mhzkb/another-space/1.5/and-another-space/and-another-space.kicad_sch

## KiCad design 1.5/and-another-space/and-another-space.kicad_sch (2025-10-27)

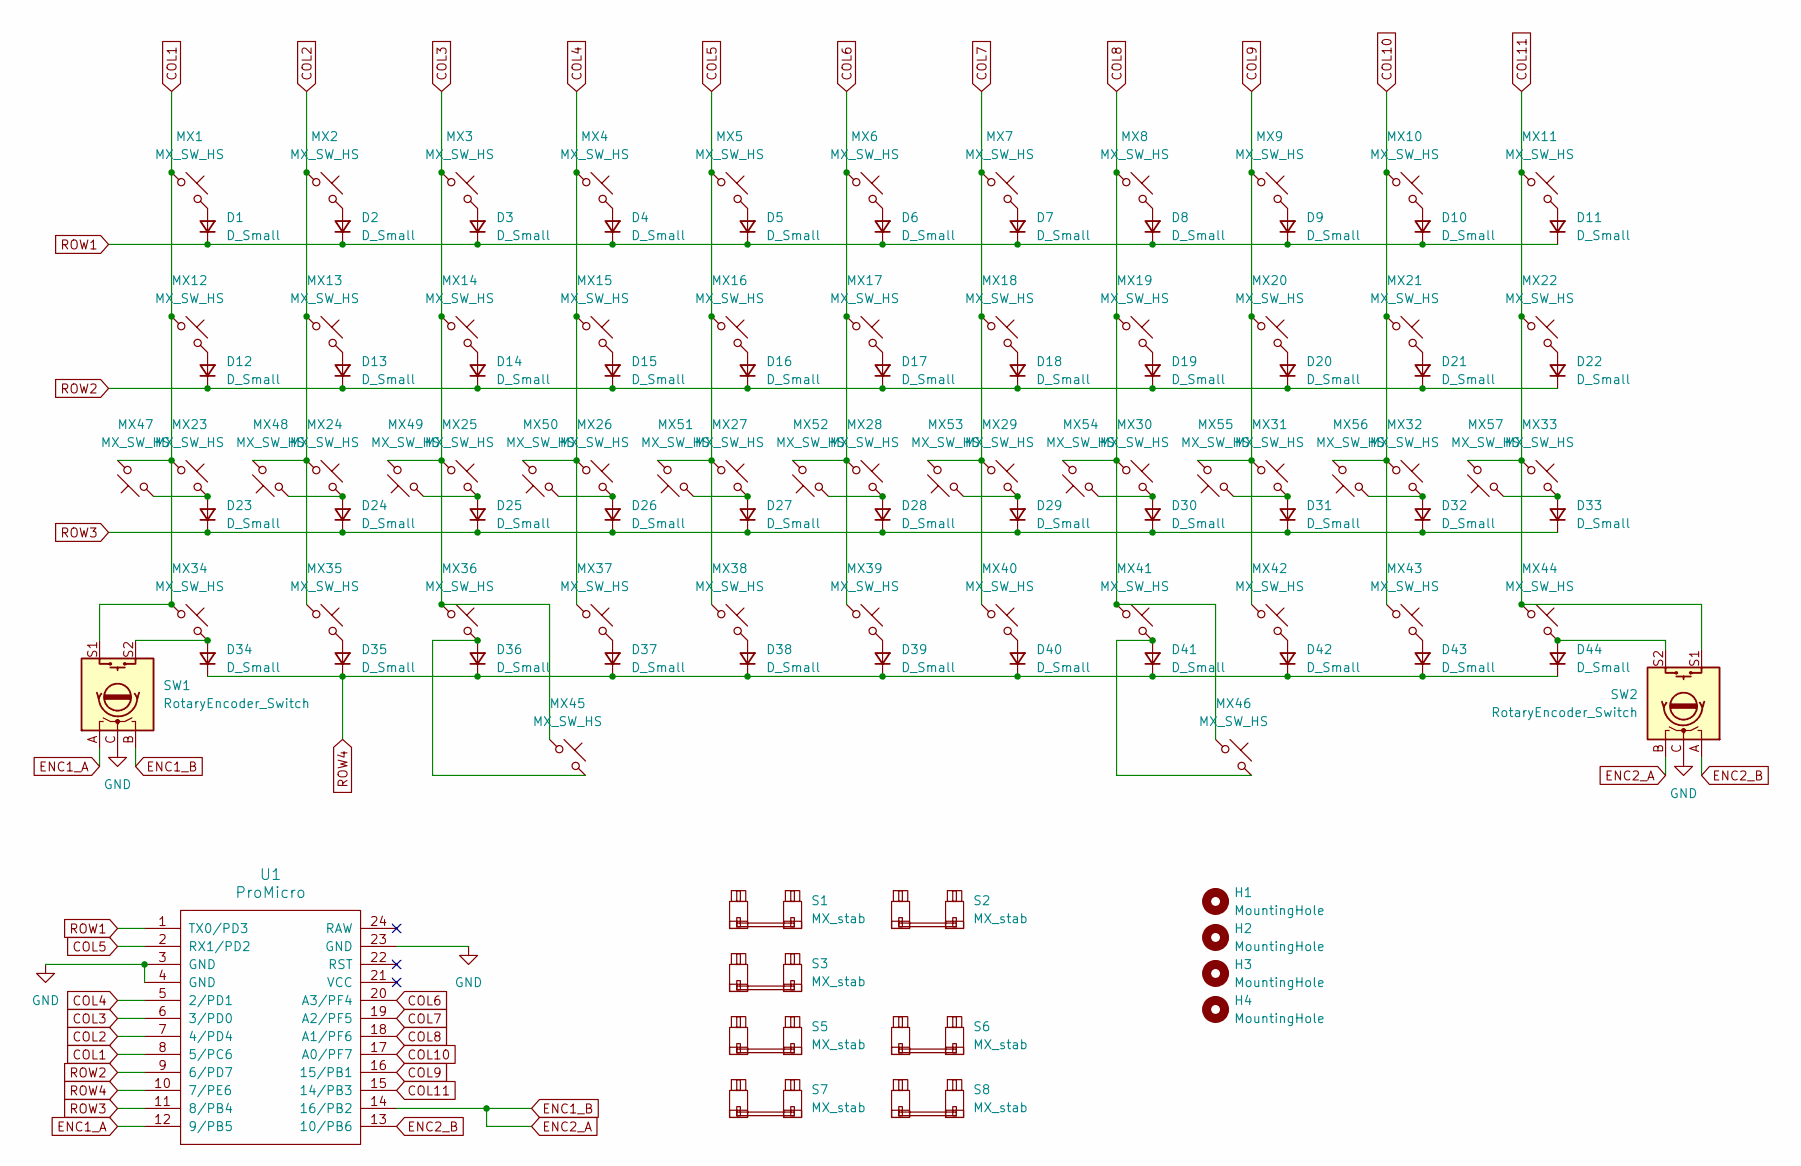
[picture p8: schematic and-another-space.kicad_sch]

Parts:
D1, D2, D3, D4, D5, D6, D7, D8, D9, D10, D11, D12, D13, D14, D15, D16, D17, D18, D19, D20, D21, D22, D23, D24, D25, D26, D27, D28, D29, D30, D31, D32, D33, D34, D35, D36, D37, D38, D39, D40, D41, D42, D43, D44: D_Small; D_SOD-123
H1, H2, H3, H4: MountingHole; MountingHole_2.2mm_M2_Pad
MX1, MX2, MX3, MX4, MX5, MX6, MX7, MX8, MX9, MX10, MX11, MX12, MX13, MX14, MX15, MX16, MX17, MX18, MX19, MX20, MX21, MX22, MX23, MX24, MX25, MX26, MX27, MX28, MX29, MX30, MX31, MX32, MX33, MX34, MX35, MX36, MX37, MX38, MX39, MX40, MX41, MX42, MX43, MX44, MX45, MX46, MX48, MX49, MX50, MX51, MX52, MX53, MX54, MX55, MX56: MX_SW_HS; SW_MX_HS_CPG151101S11_1u
MX47, MX57: MX_SW_HS; SW_MX_HS_CPG151101S11_1.5u
S1, S2, S3, S8: MX_stab; STAB_MX_P_7u
S5, S6: MX_stab; STAB_MX_P_2u
S7: MX_stab; STAB_MX_P_6u
SW1, SW2: RotaryEncoder_Switch; RotaryEncoder_EC11-no-legs
U1: ProMicro; ArduinoProMicro

Connections:
COL1: MX1.1, MX12.1, MX23.1, MX34.1, MX47.2, SW1.S1, U1.8 (5/PC6)
COL2: MX2.1, MX13.1, MX24.1, MX35.1, MX48.2, U1.7 (4/PD4)
COL3: MX3.1, MX14.1, MX25.1, MX36.1, MX45.1, MX49.2, U1.6 (3/PD0)
COL4: MX4.1, MX15.1, MX26.1, MX37.1, MX50.2, U1.5 (2/PD1)
COL5: MX5.1, MX16.1, MX27.1, MX38.1, MX51.2, U1.2 (RX1/PD2)
COL6: MX6.1, MX17.1, MX28.1, MX39.1, MX52.2, U1.20 (A3/PF4)
COL7: MX7.1, MX18.1, MX29.1, MX40.1, MX53.2, U1.19 (A2/PF5)
COL8: MX8.1, MX19.1, MX30.1, MX41.1, MX46.1, MX54.2, U1.18 (A1/PF6)
COL9: MX9.1, MX20.1, MX31.1, MX42.1, MX55.2, U1.16 (15/PB1)
COL10: MX10.1, MX21.1, MX32.1, MX43.1, MX56.2, U1.17 (A0/PF7)
COL11: MX11.1, MX22.1, MX33.1, MX44.1, MX57.2, SW2.S1, U1.15 (14/PB3)
ENC1_A: SW1.A, U1.12 (9/PB5)
ENC1_B: SW1.B, SW2.B, U1.14 (16/PB2)
ENC2_B: SW2.A, U1.13 (10/PB6)
GND: SW1.C, SW2.C, U1.3 (GND), U1.4 (GND), U1.23 (GND)
unnamed: D1.2 (A), MX1.2
unnamed: D2.2 (A), MX2.2
unnamed: D3.2 (A), MX3.2
unnamed: D4.2 (A), MX4.2
unnamed: D5.2 (A), MX5.2
unnamed: D6.2 (A), MX6.2
unnamed: D7.2 (A), MX7.2
unnamed: D8.2 (A), MX8.2
unnamed: D9.2 (A), MX9.2
unnamed: D10.2 (A), MX10.2
unnamed: D11.2 (A), MX11.2
unnamed: D12.2 (A), MX12.2
unnamed: D13.2 (A), MX13.2
unnamed: D14.2 (A), MX14.2
unnamed: D15.2 (A), MX15.2
unnamed: D16.2 (A), MX16.2
unnamed: D17.2 (A), MX17.2
unnamed: D18.2 (A), MX18.2
unnamed: D19.2 (A), MX19.2
unnamed: D20.2 (A), MX20.2
unnamed: D21.2 (A), MX21.2
unnamed: D22.2 (A), MX22.2
unnamed: D23.2 (A), MX23.2, MX47.1
unnamed: D24.2 (A), MX24.2, MX48.1
unnamed: D25.2 (A), MX25.2, MX49.1
unnamed: D26.2 (A), MX26.2, MX50.1
unnamed: D27.2 (A), MX27.2, MX51.1
unnamed: D28.2 (A), MX28.2, MX52.1
unnamed: D29.2 (A), MX29.2, MX53.1
unnamed: D30.2 (A), MX30.2, MX54.1
unnamed: D31.2 (A), MX31.2, MX55.1
unnamed: D32.2 (A), MX32.2, MX56.1
unnamed: D33.2 (A), MX33.2, MX57.1
unnamed: D34.2 (A), MX34.2, SW1.S2
unnamed: D35.2 (A), MX35.2
unnamed: D36.2 (A), MX36.2, MX45.2
unnamed: D37.2 (A), MX37.2
unnamed: D38.2 (A), MX38.2
unnamed: D39.2 (A), MX39.2
unnamed: D40.2 (A), MX40.2
unnamed: D41.2 (A), MX41.2, MX46.2
unnamed: D42.2 (A), MX42.2
unnamed: D43.2 (A), MX43.2
unnamed: D44.2 (A), MX44.2, SW2.S2
ROW1: D1.1 (K), D2.1 (K), D3.1 (K), D4.1 (K), D5.1 (K), D6.1 (K), D7.1 (K), D8.1 (K), D9.1 (K), D10.1 (K), D11.1 (K), U1.1 (TX0/PD3)
ROW2: D12.1 (K), D13.1 (K), D14.1 (K), D15.1 (K), D16.1 (K), D17.1 (K), D18.1 (K), D19.1 (K), D20.1 (K), D21.1 (K), D22.1 (K), U1.9 (6/PD7)
ROW3: D23.1 (K), D24.1 (K), D25.1 (K), D26.1 (K), D27.1 (K), D28.1 (K), D29.1 (K), D30.1 (K), D31.1 (K), D32.1 (K), D33.1 (K), U1.11 (8/PB4)
ROW4: D34.1 (K), D35.1 (K), D36.1 (K), D37.1 (K), D38.1 (K), D39.1 (K), D40.1 (K), D41.1 (K), D42.1 (K), D43.1 (K), D44.1 (K), U1.10 (7/PE6)
